NagyGiliszt/Incubator_2/sw/src/chars.h

#ifndef CHARS_H
#define CHARS_H

byte CHARS[19][8] = {
    //0 - Á
    {
		B00010,
		B00100,
		B01110,
		B10001,
		B11111,
		B10001,
		B10001,
		B00000
    },
    //1 - É
    {
		B00010,
		B00100,
		B11111,
		B10000,
		B11110,
		B10000,
		B11111,
		B00000
    },
    //2 - Í
    {
		B00010,
		B00100,
		B01110,
		B00100,
		B00100,
		B00100,
		B01110,
		B00000
    },
    //3 - Ú
    {
		B00010,
		B00100,
		B10001,
		B10001,
		B10001,
		B10001,
		B01110,
		B00000
    },
    //4 - Ü
    {
		B01010,
		B00000,
		B10001,
		B10001,
		B10001,
		B10001,
		B01110,
		B00000
    },
    //5 - Ó
    {
		B00010,
		B00100,
		B01110,
		B10001,
		B10001,
		B10001,
		B01110,
		B00000
    },
    //6 - Ö
    {
        B01010,
        B00000,
        B01110,
        B10001,
        B10001,
        B10001,
        B01110,
        B00000
    },
    //7 - Ő
    {
        B00101,
        B01010,
        B01110,
        B10001,
        B10001,
        B10001,
        B01110,
        B00000
    },
    //8 - Ű
    {
        B00101,
        B01010,
        B10001,
        B10001,
        B10001,
        B10001,
        B01110,
        B00000
    },
    
    //9 - á
    {
		B00010,
		B00100,
		B01110,
		B00001,
		B01111,
		B10001,
		B01111,
		B00000
    },
    
    //10 - é
    {
		B00010,
		B00100,
		B01110,
		B10001,
		B11111,
		B10000,
		B01110,
		B00000
    },
    
    //11 - í
    {
		B00010,
		B00100,
		B00000,
		B01100,
		B00100,
		B00100,
		B01110,
		B00000
    },
    
    //12 - ú
    {
		B00010,
		B00100,
		B10001,
		B10001,
		B10001,
		B10011,
		B01101,
		B00000
    },
    
    //13 - ü
    {
		B01010,
		B00000,
		B10001,
		B10001,
		B10001,
		B10011,
		B01101,
		B00000
    },
    
    //14 - ó
    {
		B00010,
		B00100,
		B01110,
		B10001,
		B10001,
		B10001,
		B01110,
		B00000
    },
    
    //15 - ö
    {
		B01010,
		B00000,
		B01110,
		B10001,
		B10001,
		B10001,
		B01110,
		B00000
    },
    
    //16 - ő
    {
		B00101,
		B01010,
		B01110,
		B10001,
		B10001,
		B10001,
		B01110,
		B00000
    },
    
    //17 - ű
    {
		B00101,
		B01010,
		B10001,
		B10001,
		B10001,
		B10011,
		B01101,
		B00000
    }, 
	    //18 - smiley
    {
		B00000,
		B00000,
		B10001,
		B00000,
		B00000,
		B10001,
		B01110,
		B00000
    }
};

#endif
